Elensif/Modulo-de-dibujo/Caja electrónica/Fotografía A.jpg

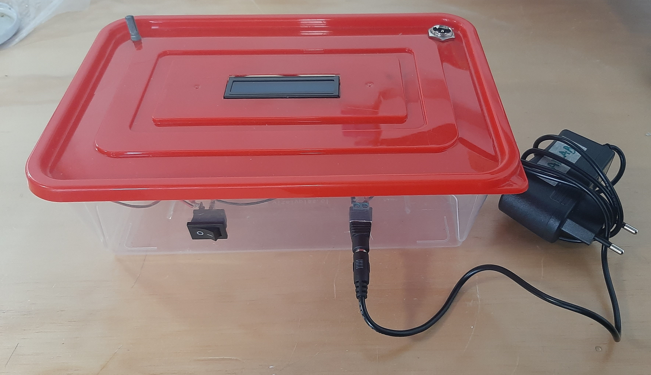
Caja electrónica/Fotografía A.jpg
