Elensif/Modulo-de-dibujo/Modelos 3D/Fotografías/4. Prototipo detalle.jpg

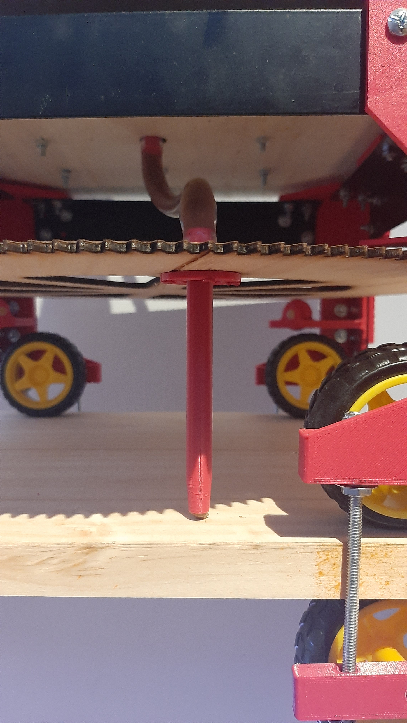
Modelos 3D/Fotografías/4. Prototipo detalle.jpg
