Elensif/Modulo-de-dibujo/Modelos 3D/Fotografías/6. Ruedas.jpg

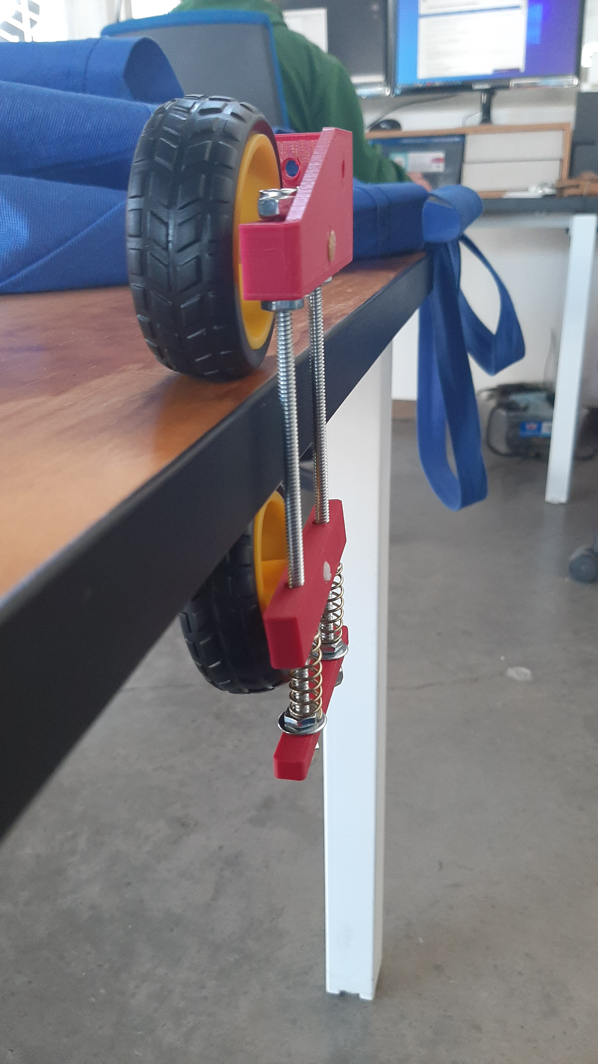
Modelos 3D/Fotografías/6. Ruedas.jpg
