Elensif/Modulo-de-dibujo/Modelos 3D/Fotografías/8. Alineador.jpeg

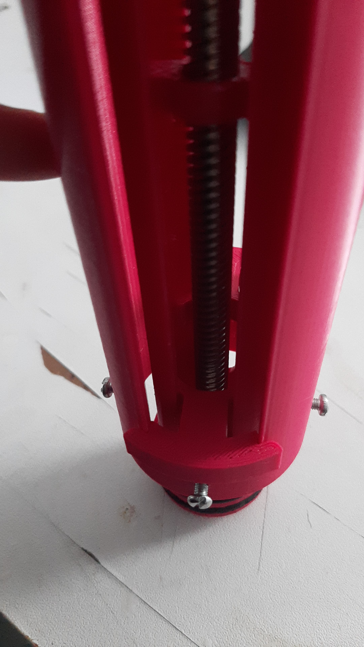
Modelos 3D/Fotografías/8. Alineador.jpeg
