Elensif/Modulo-de-dibujo/Modelos 3D/Ensamblaje/Componentes Extrusor.jpg

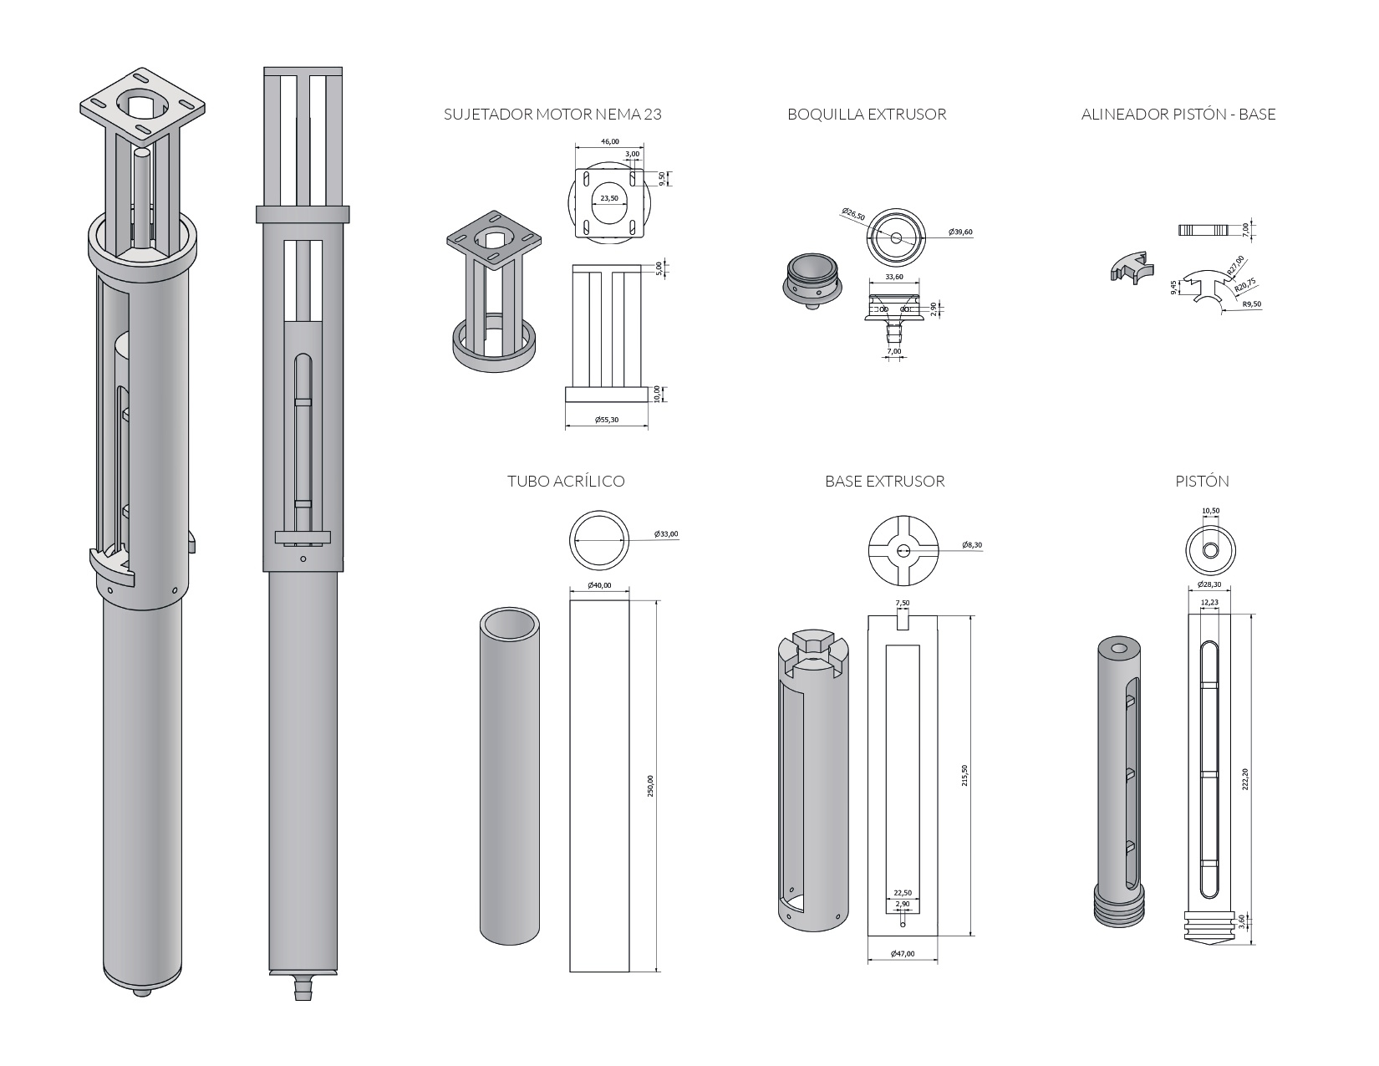
Modelos 3D/Ensamblaje/Componentes Extrusor.jpg
