Elensif/Modulo-de-dibujo/Modelos 3D/Ensamblaje/Componentes Módulo A.jpg

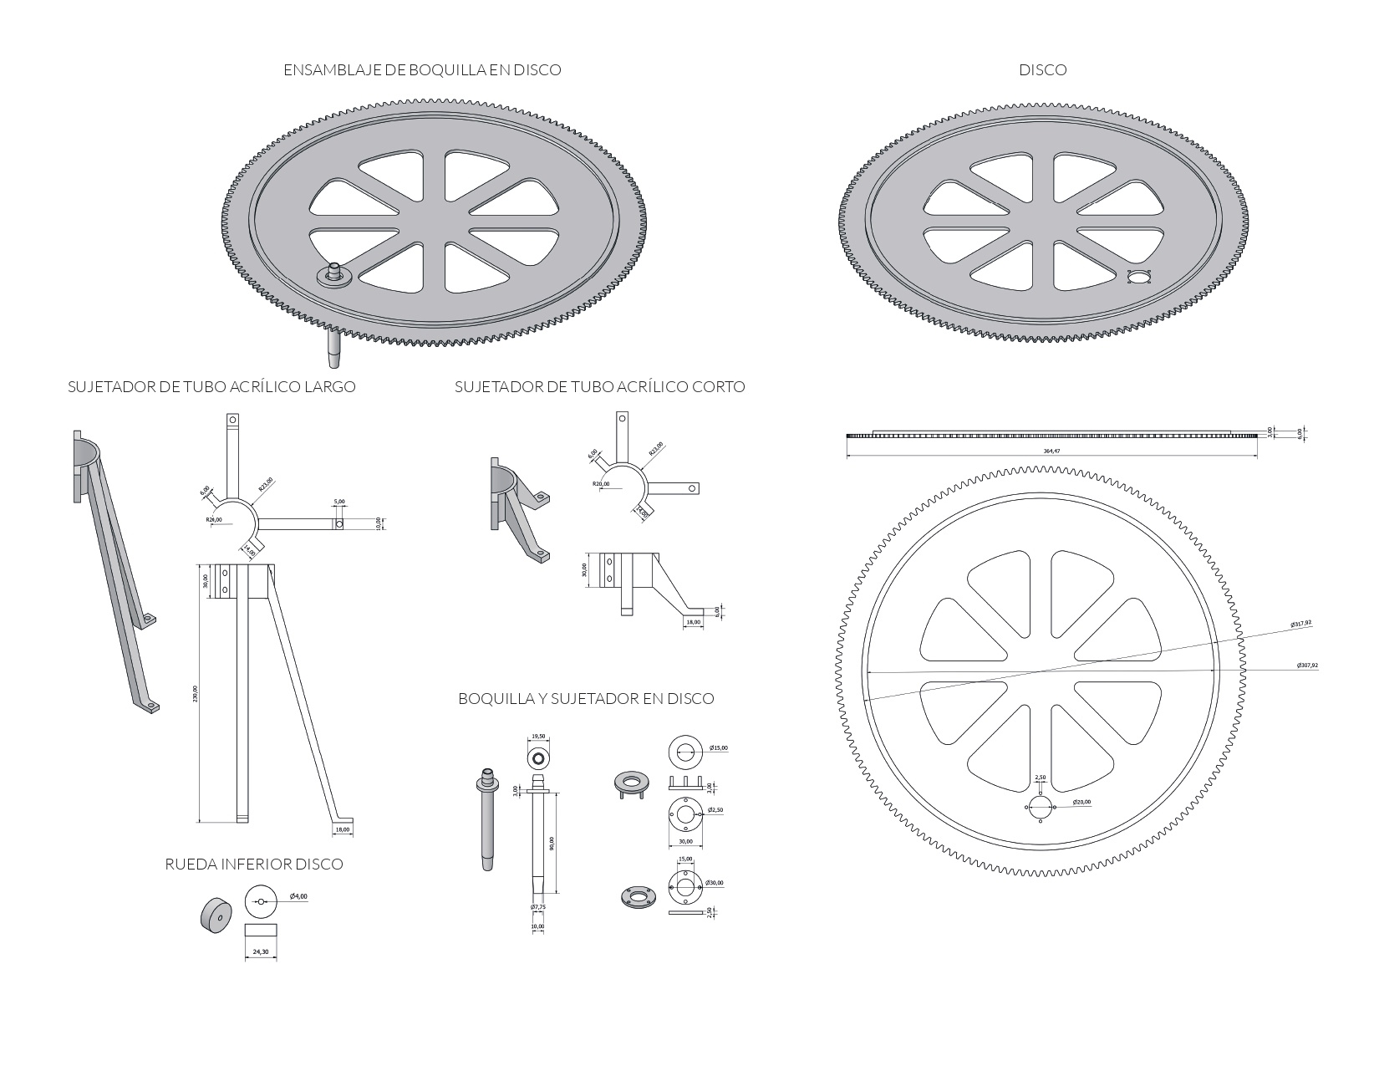
Modelos 3D/Ensamblaje/Componentes Módulo A.jpg
