Elensif/Modulo-de-dibujo/Modelos 3D/Ensamblaje/Componentes Módulo B.jpg

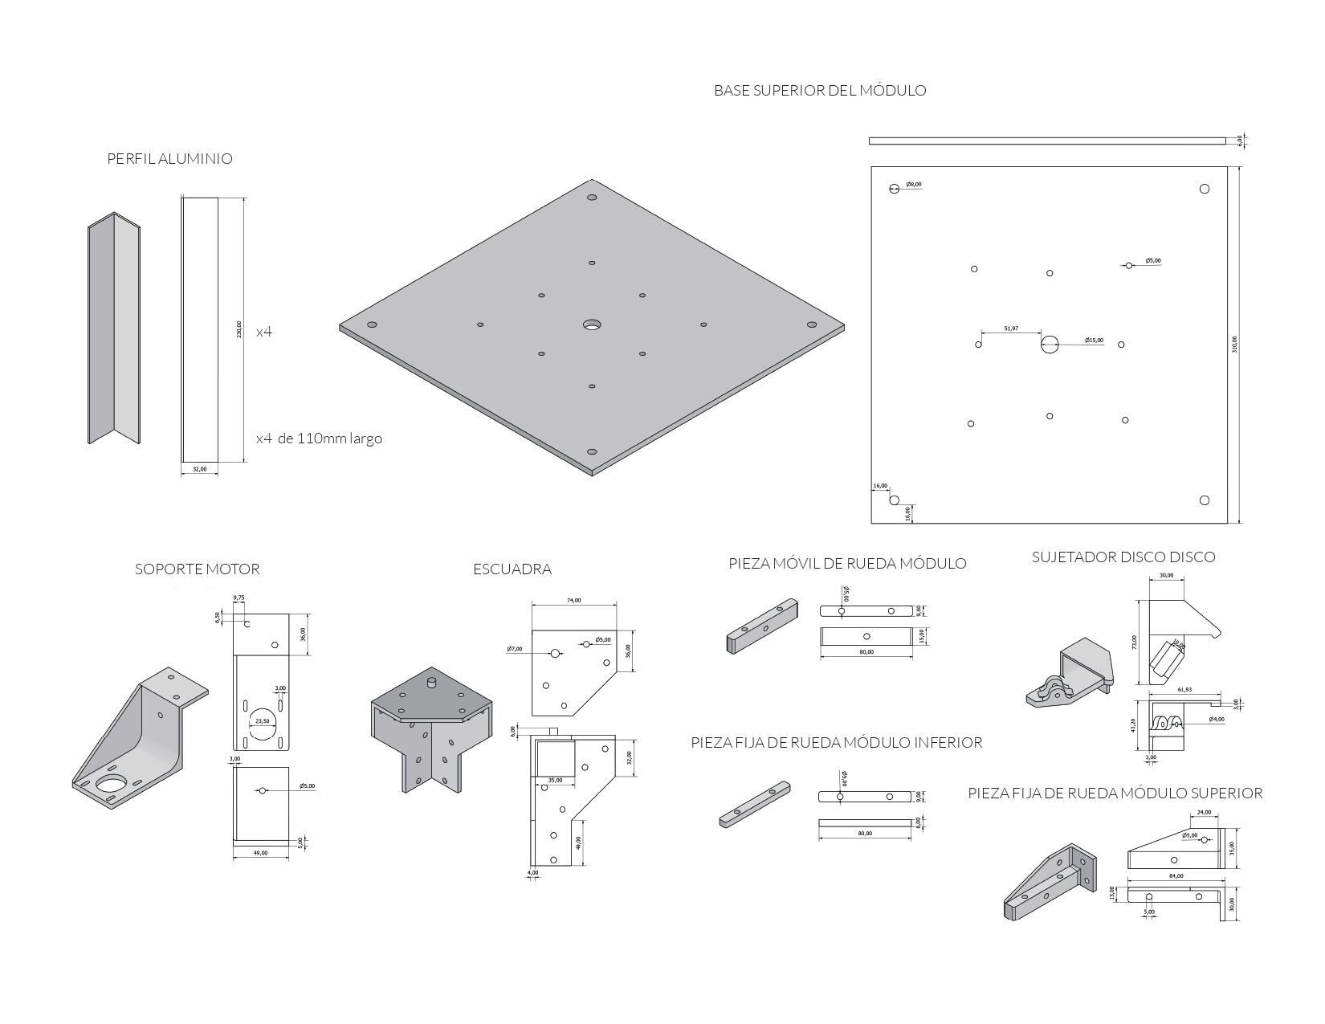
Modelos 3D/Ensamblaje/Componentes Módulo B.jpg
