Elensif/Modulo-de-dibujo/Modelos 3D/Módulo/Base superior/Sujetador Extrusor B.stl

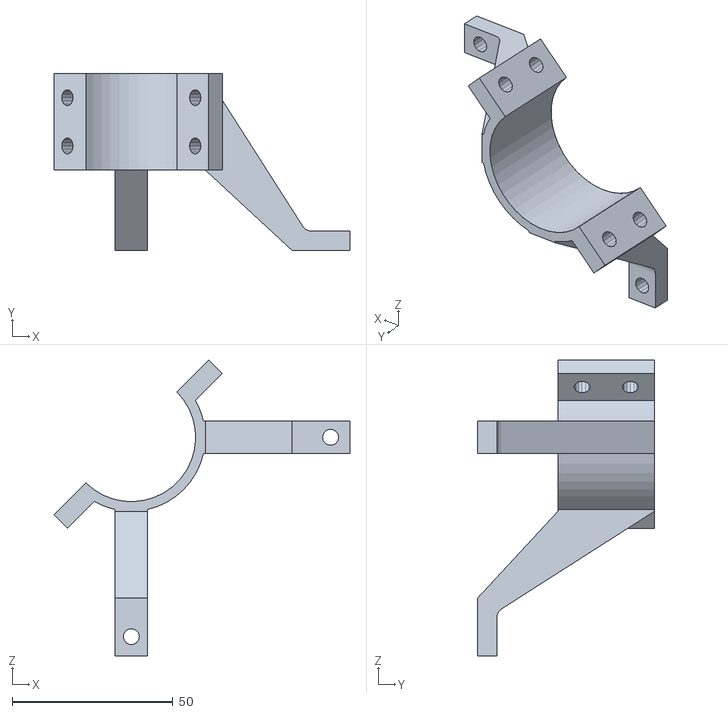
[picture p28: CAD file, 2023-12-13]
Modelos 3D/Módulo/Base superior/Sujetador Extrusor B.stl
92.0 x 55.0 x 92.0
