Elensif/Modulo-de-dibujo/Modelos 3D/Módulo/Ruedas módulo/Pieza móvil.stl

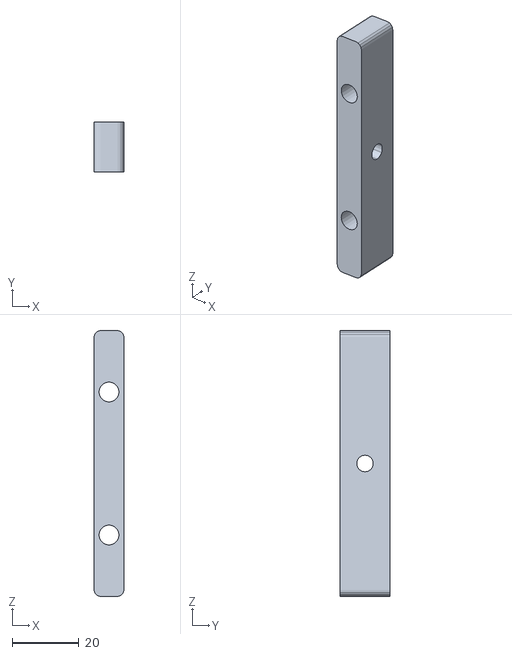
[picture p29: CAD file, 2023-12-13]
Modelos 3D/Módulo/Ruedas módulo/Pieza móvil.stl
9.00 x 15.0 x 80.0
