Elensif/Modulo-de-dibujo/Modelos 3D/Extrusor/Base motor Nema17.stl

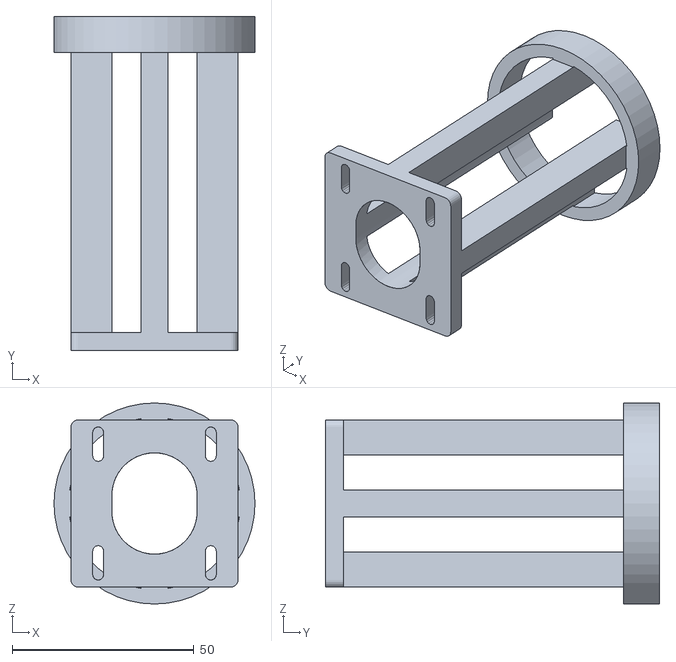
[picture p30: CAD file, 2023-12-13]
Modelos 3D/Extrusor/Base motor Nema17.stl
55.3 x 92.0 x 55.3
