Elensif/Modulo-de-dibujo/Modelos 3D/Módulo/Ruedas módulo/Tope inferior.stl

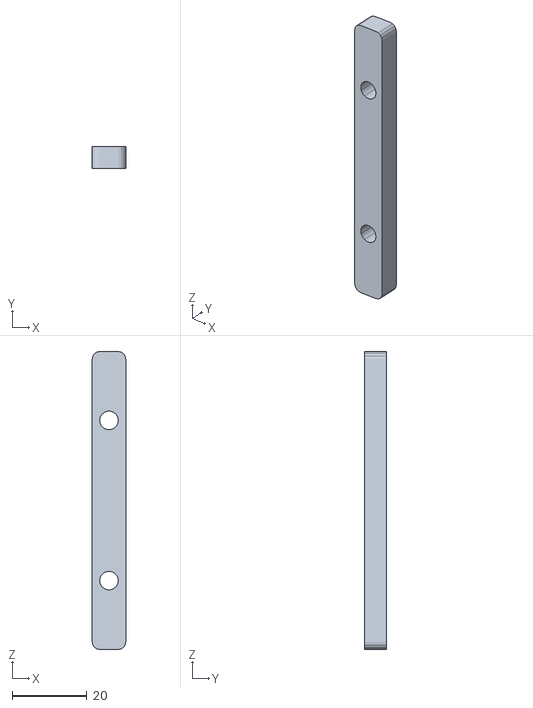
[picture p31: CAD file, 2023-12-13]
Modelos 3D/Módulo/Ruedas módulo/Tope inferior.stl
9.00 x 6.00 x 80.0
