Elensif/Modulo-de-dibujo/Modelos 3D/Extrusor/Base motor Nema23.stl

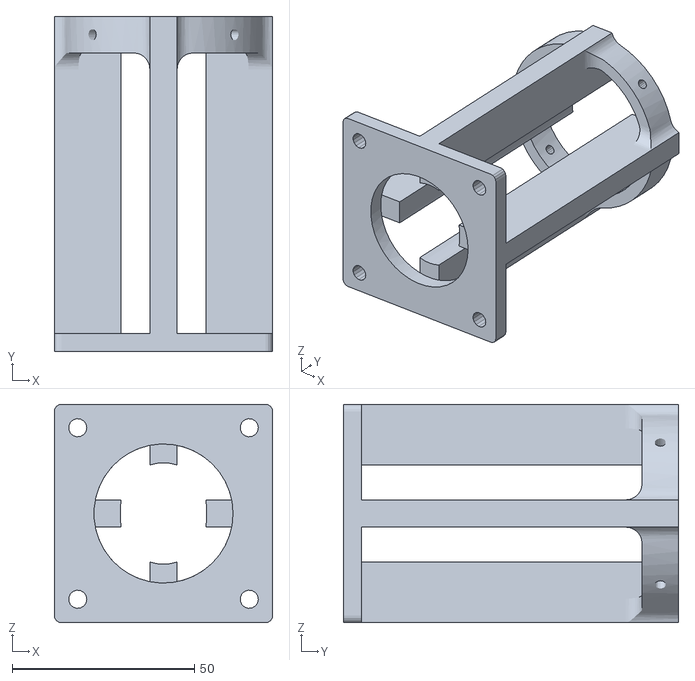
[picture p32: CAD file, 2023-12-13]
Modelos 3D/Extrusor/Base motor Nema23.stl
60.0 x 92.0 x 60.0
