Elensif/Modulo-de-dibujo/Modelos 3D/Módulo/Ruedas módulo/Pasador ruedas.stl

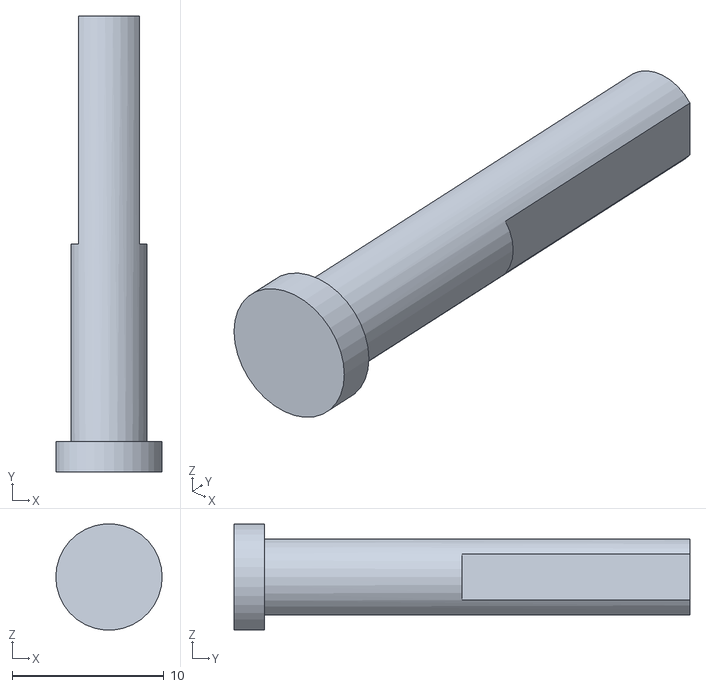
[picture p33: CAD file, 2023-12-13]
Modelos 3D/Módulo/Ruedas módulo/Pasador ruedas.stl
7.00 x 30.0 x 6.97
