Elensif/Modulo-de-dibujo/Modelos 3D/Extrusor/Base A.stl

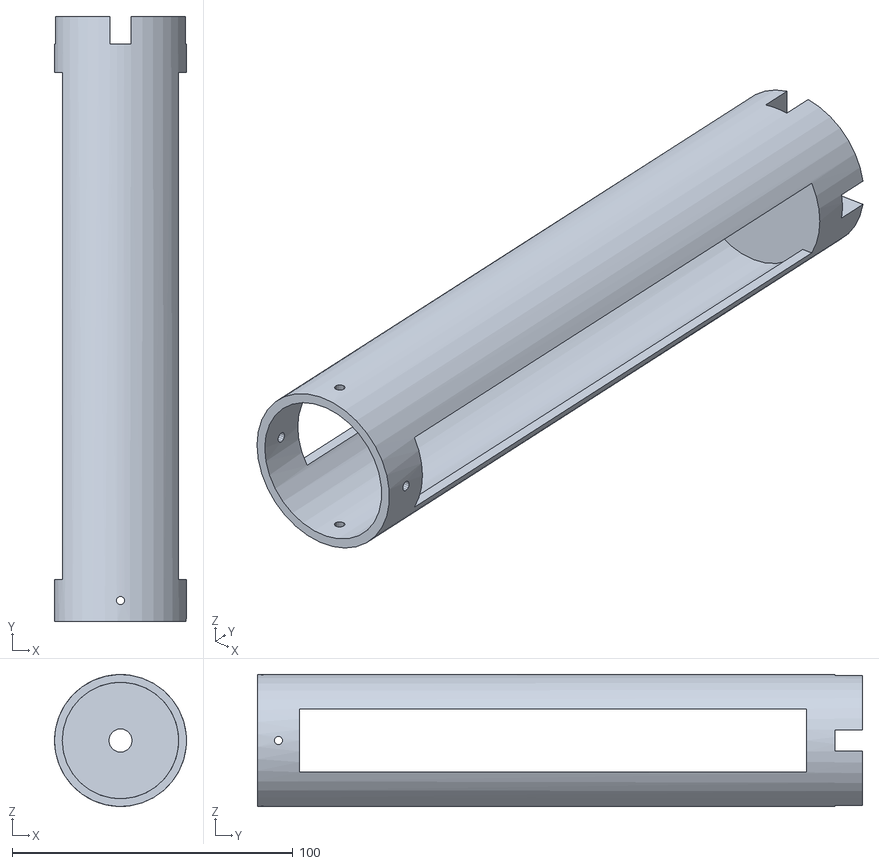
[picture p34: CAD file, 2023-12-13]
Modelos 3D/Extrusor/Base A.stl
47.0 x 215.5 x 47.0
