Elensif/Modulo-de-dibujo/Caja electrónica/Circuito armado.png

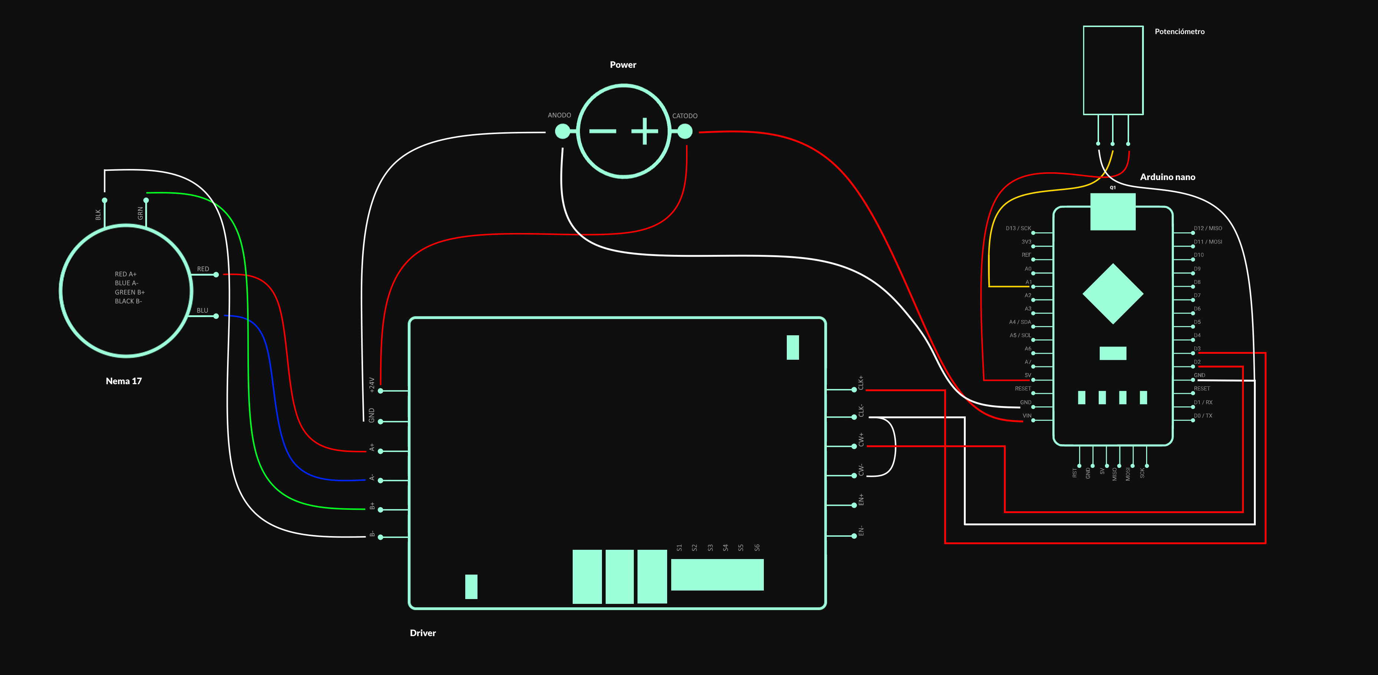
Caja electrónica/Circuito armado.png
