Elensif/Modulo-de-dibujo/Modelos 3D/Ensamblaje/Referencia módulo.jpg

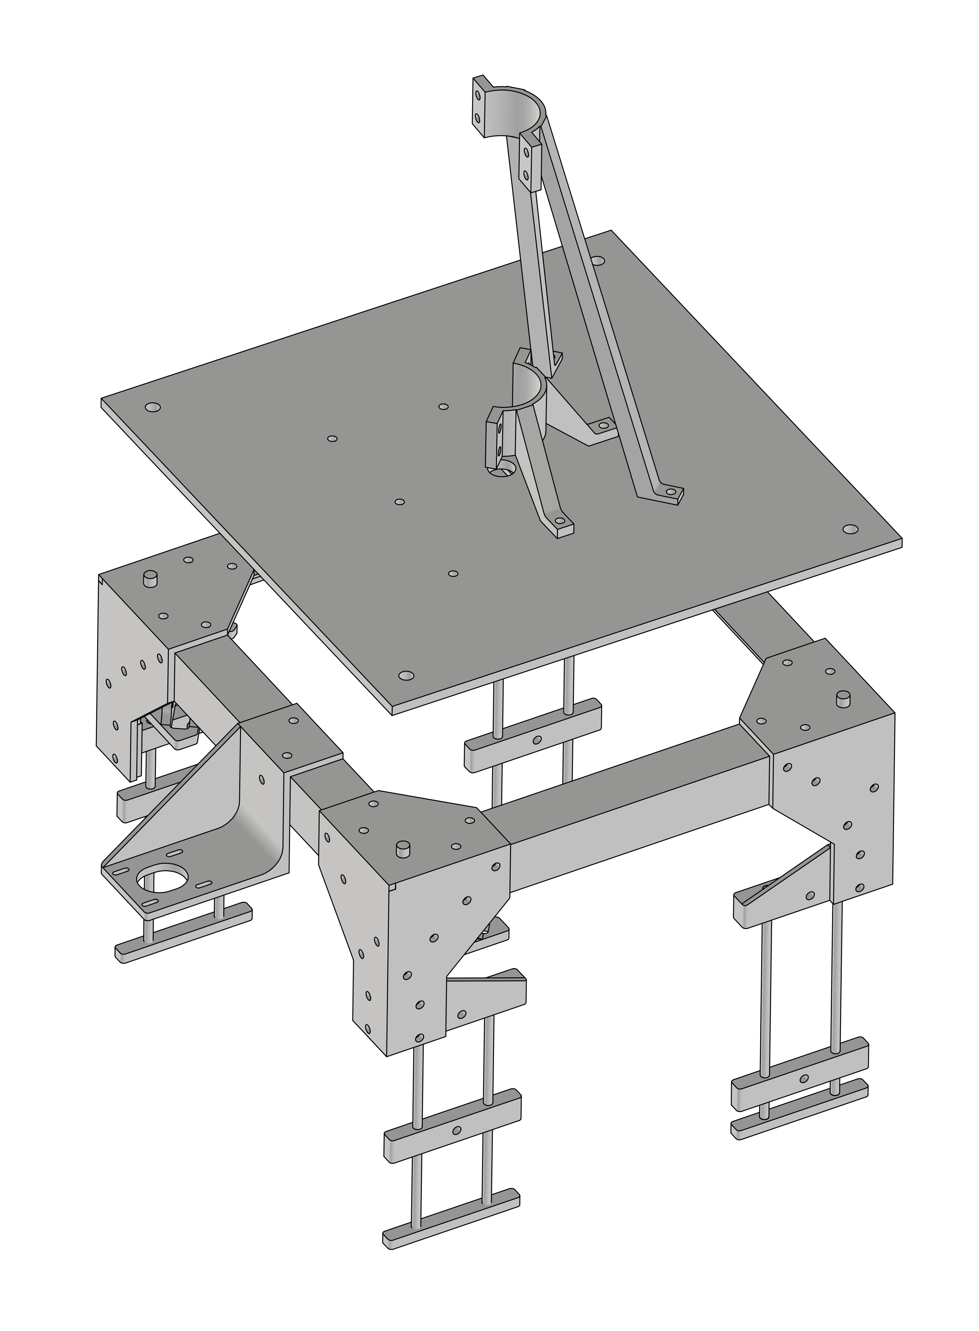
Modelos 3D/Ensamblaje/Referencia módulo.jpg
